svenpetersen1965/VIC-20_Character_ROM_Adapter/Rev. 0/Pictures/8974_-_Test_Vicky_Twenty.JPG

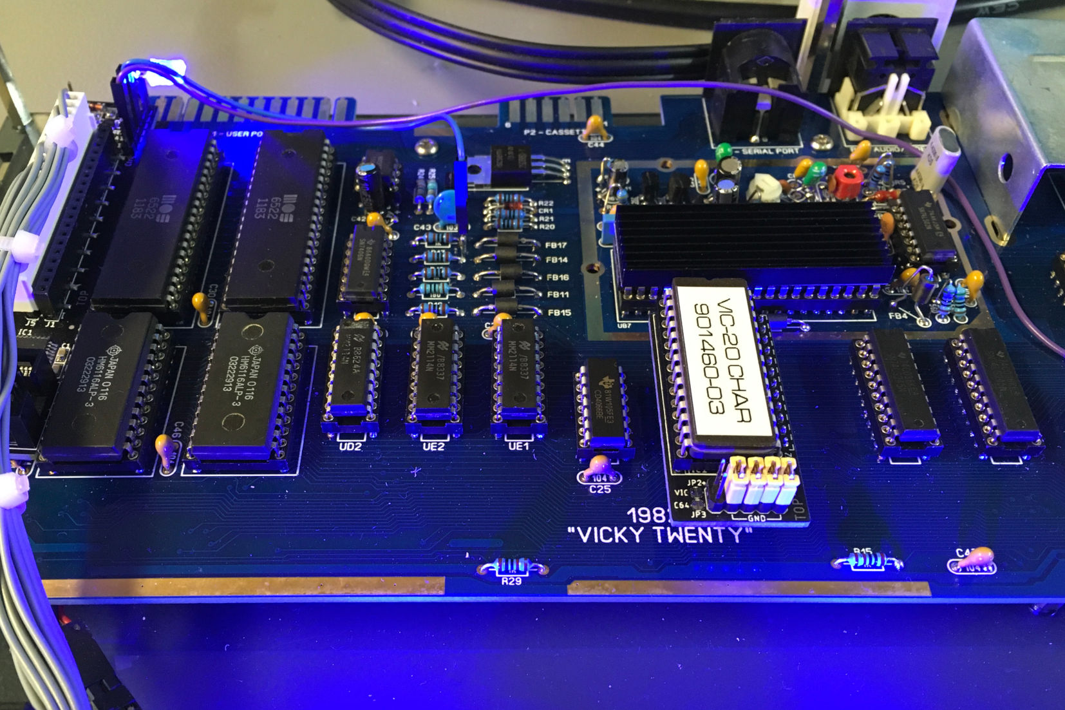
Rev. 0/Pictures/8974_-_Test_Vicky_Twenty.JPG
