svenpetersen1965/VIC-20_Character_ROM_Adapter/Rev. 0/Pictures/8998_-_Test_ASSY 324003.JPG

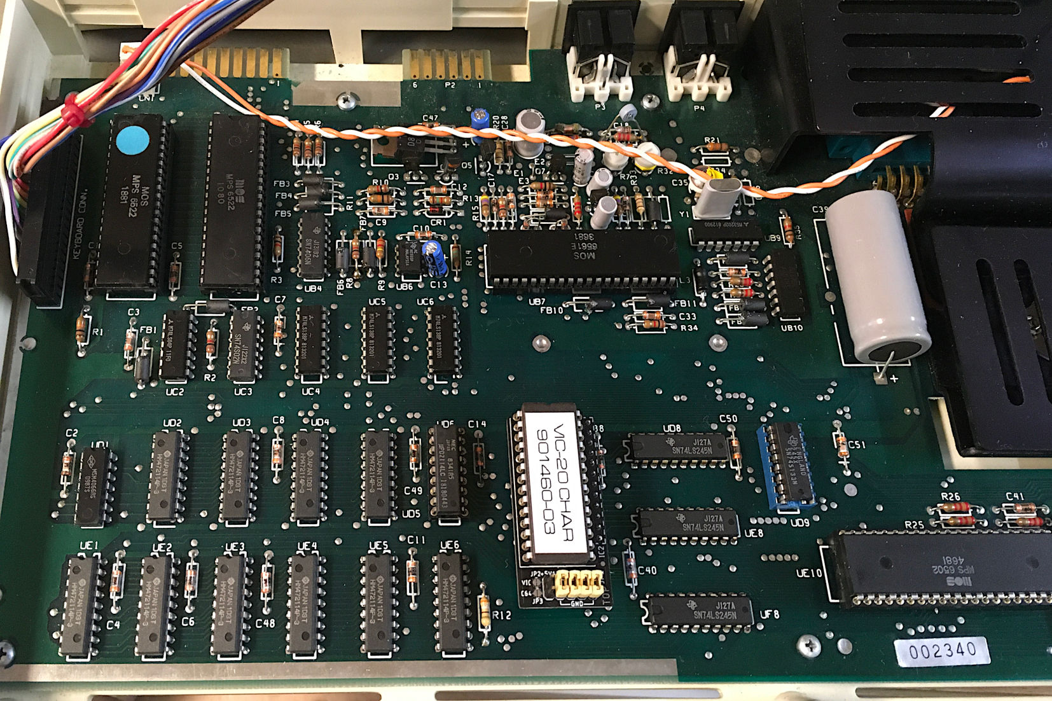
Rev. 0/Pictures/8998_-_Test_ASSY 324003.JPG
