svenpetersen1965/VIC-20_Character_ROM_Adapter/Rev. 0/Pictures/9010_-_Test_ASSY250425.JPG

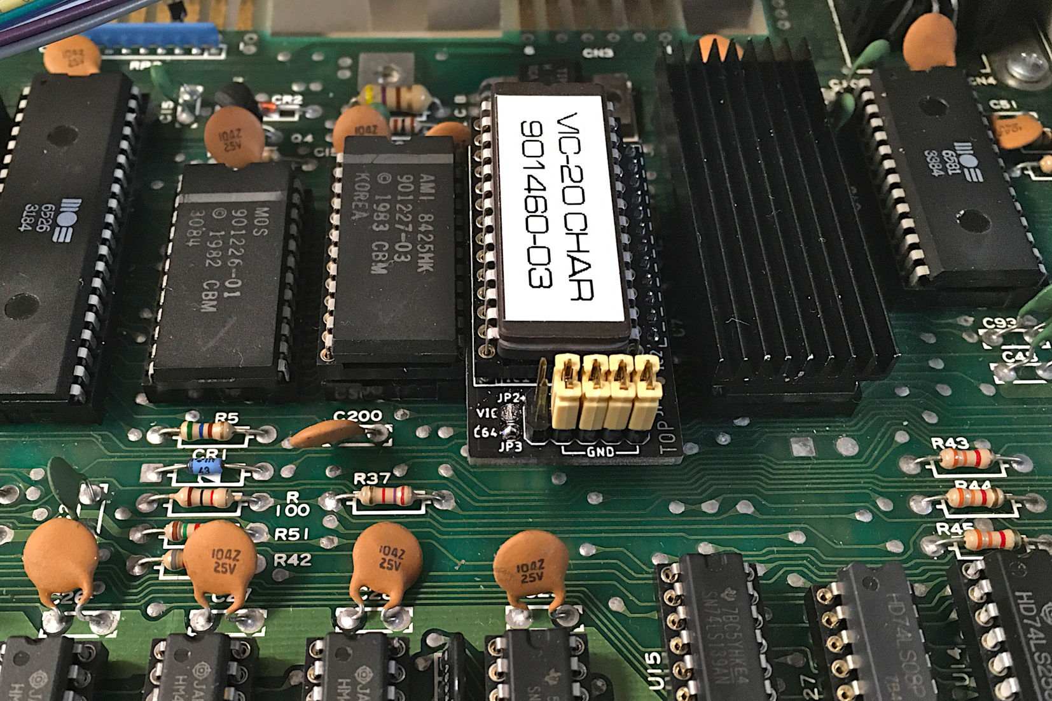
Rev. 0/Pictures/9010_-_Test_ASSY250425.JPG
