svenpetersen1965/VIC-20_Character_ROM_Adapter/Rev. 0/Pictures/9011_-_Test_ASSY250469.JPG

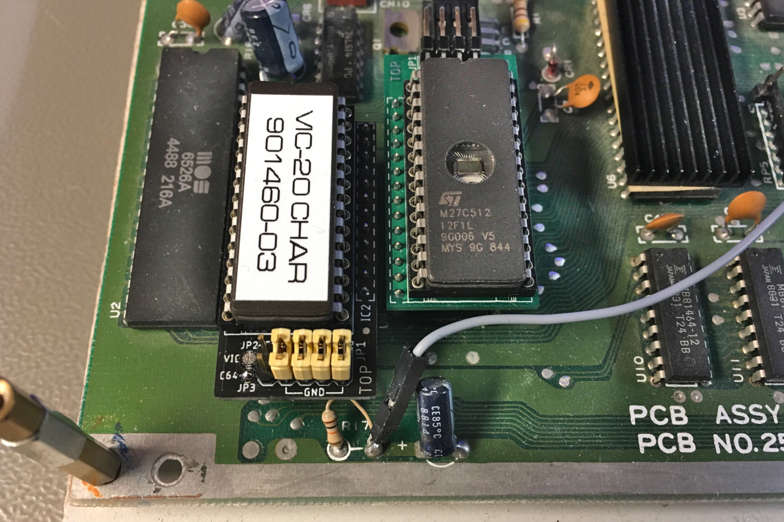
Rev. 0/Pictures/9011_-_Test_ASSY250469.JPG
